AiConde/Fund-Robo-Rover/matlab_code/tag_images/beforebridge_0.6pwm.png

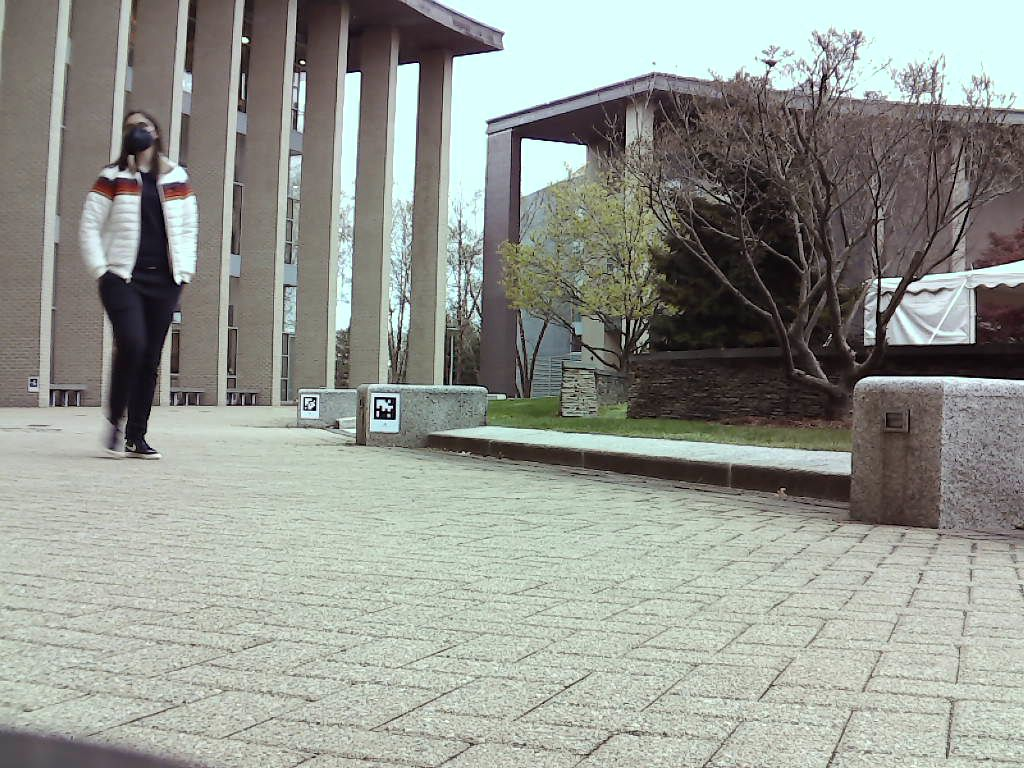
matlab_code/tag_images/beforebridge_0.6pwm.png
