AiConde/Fund-Robo-Rover/matlab_code/tag_images/beforebridge_0.6pwm_2.png

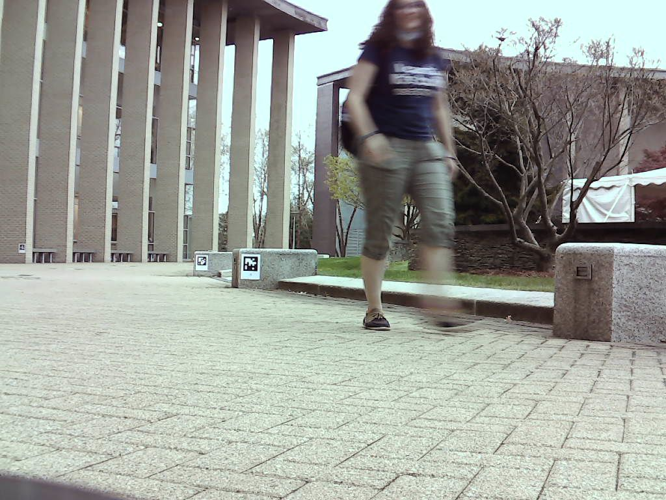
matlab_code/tag_images/beforebridge_0.6pwm_2.png
