AiConde/Fund-Robo-Rover/matlab_code/tag_images/beforebridge_0.55pwm_3.png

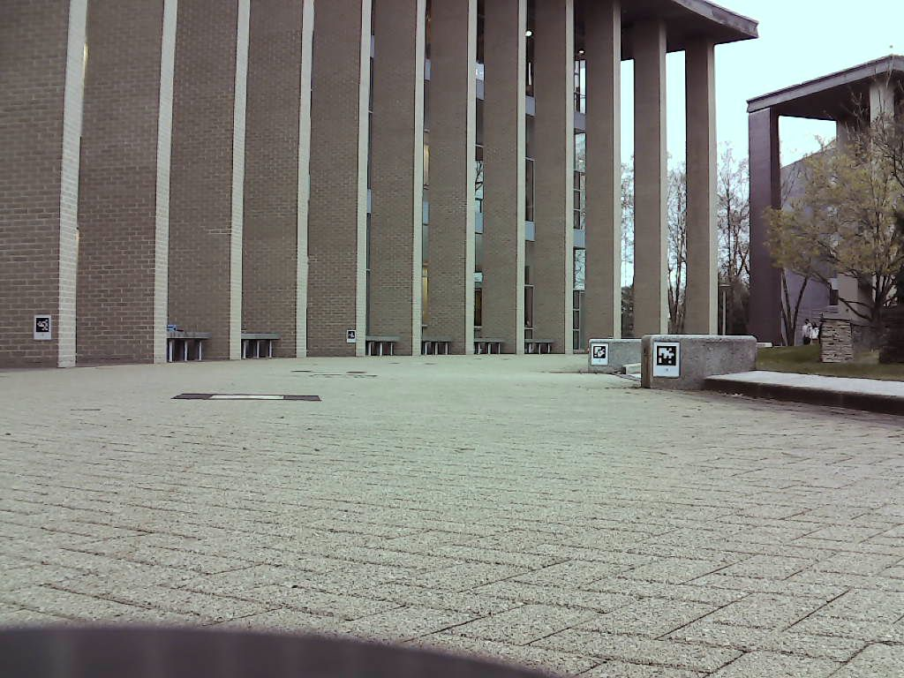
matlab_code/tag_images/beforebridge_0.55pwm_3.png
