AiConde/Fund-Robo-Rover/matlab_code/tag_images/beforecones_0.43pwm_2.png

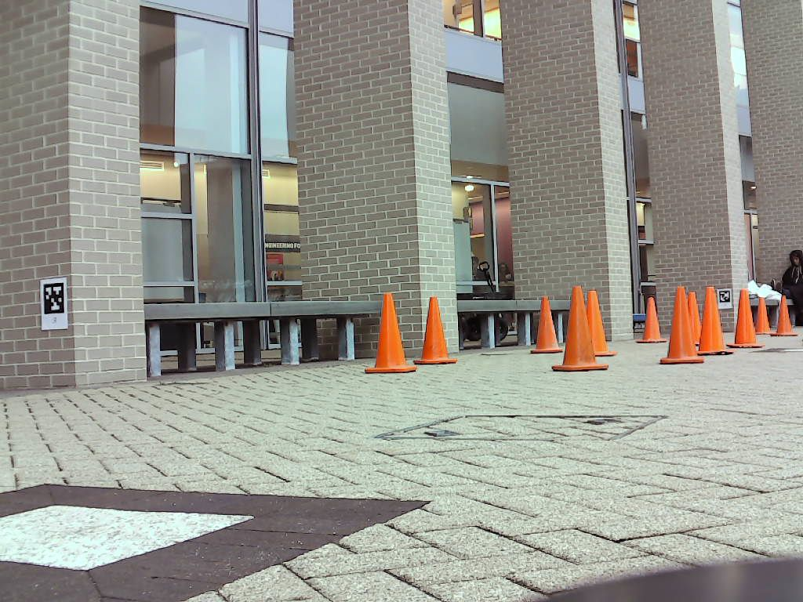
matlab_code/tag_images/beforecones_0.43pwm_2.png
