AiConde/Fund-Robo-Rover/matlab_code/tag_images/block1_0.39pwm.png

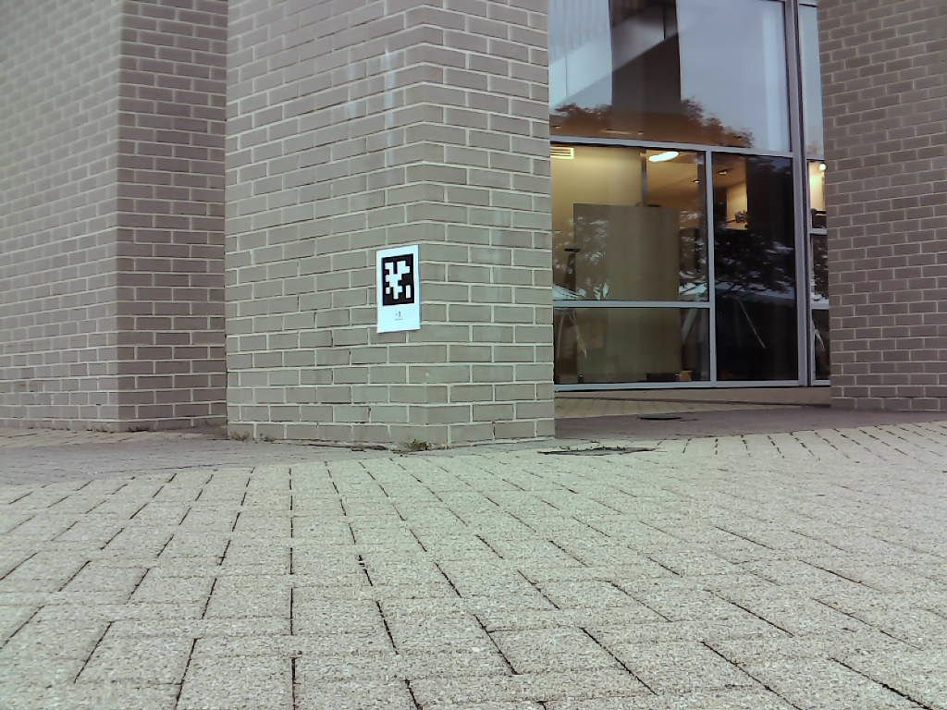
matlab_code/tag_images/block1_0.39pwm.png
