AiConde/Fund-Robo-Rover/matlab_code/tag_images/block1_0.43pwm.png

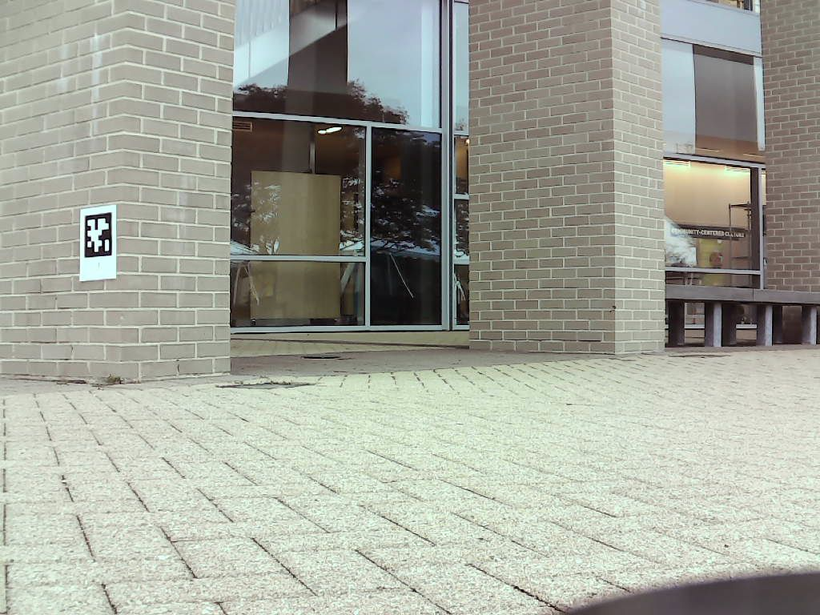
matlab_code/tag_images/block1_0.43pwm.png
