AiConde/Fund-Robo-Rover/matlab_code/tag_images/cj.png

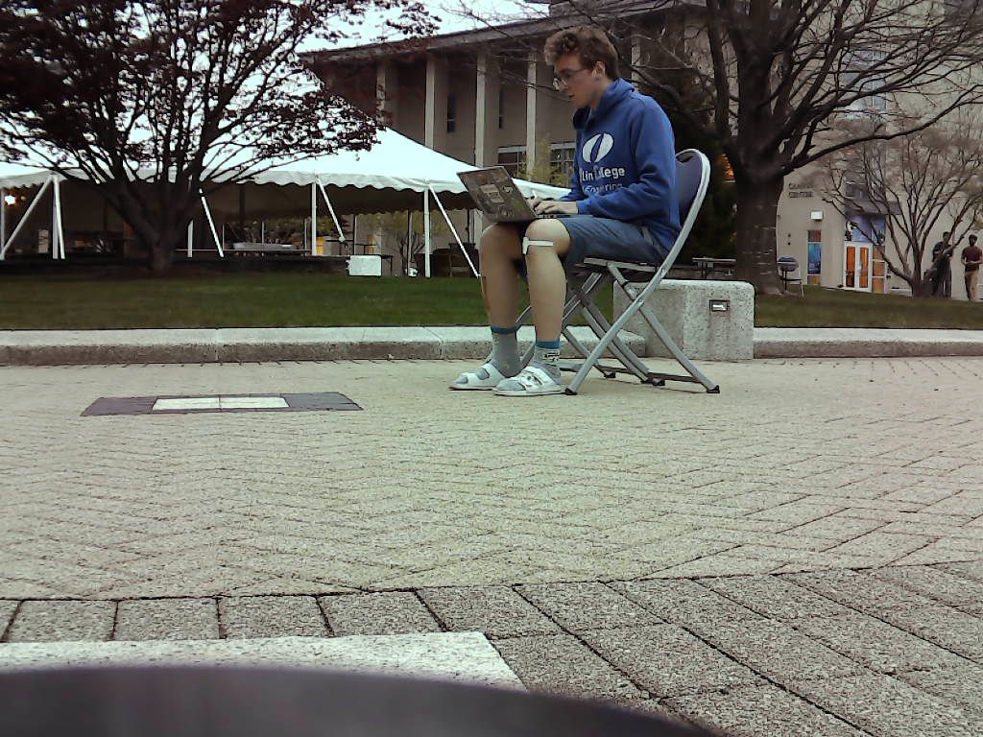
matlab_code/tag_images/cj.png
