AiConde/Fund-Robo-Rover/matlab_code/tag_images/fromdock_0.3pwm_3.png

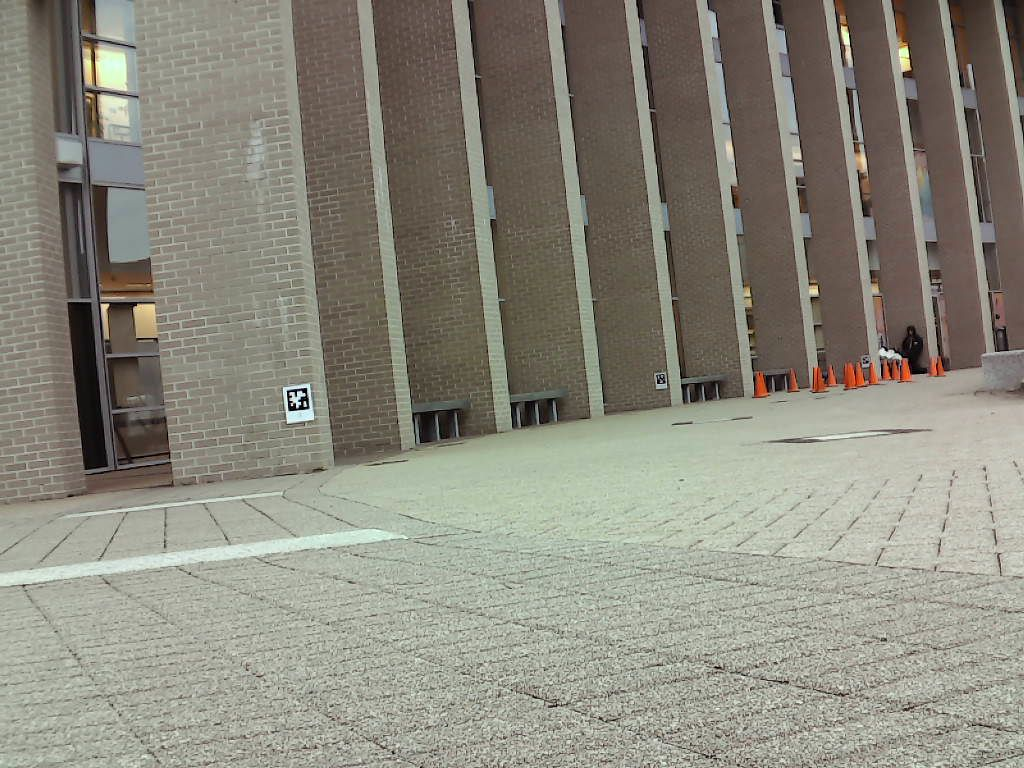
matlab_code/tag_images/fromdock_0.3pwm_3.png
