AiConde/Fund-Robo-Rover/matlab_code/tag_images/origin_north_0.5pwm.png

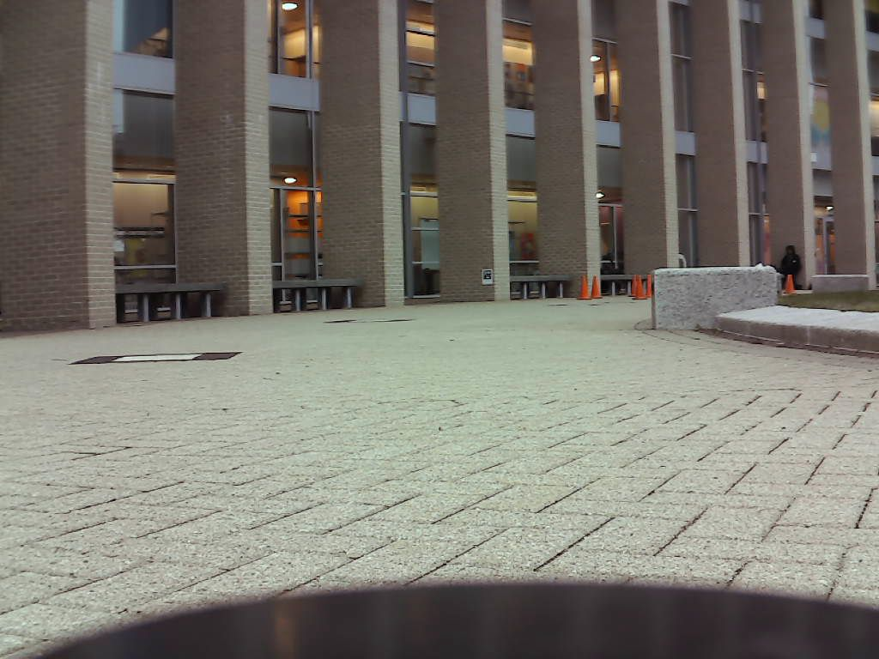
matlab_code/tag_images/origin_north_0.5pwm.png
