AiConde/Fund-Robo-Rover/matlab_code/tag_images/origin_north_0.41pwm_3.png

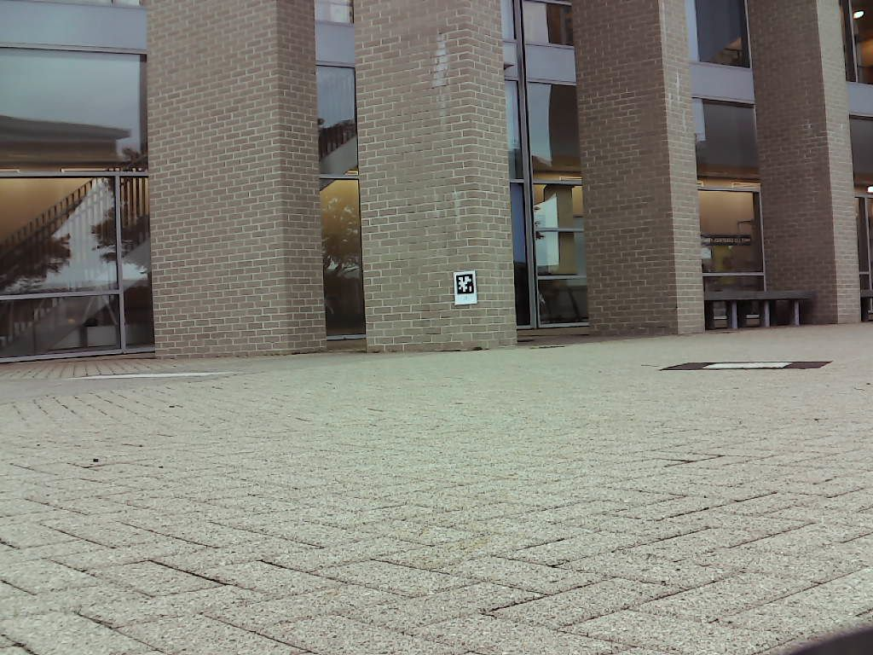
matlab_code/tag_images/origin_north_0.41pwm_3.png
