AiConde/Fund-Robo-Rover/matlab_code/tag_images/viewingdock_0.45pwm.png

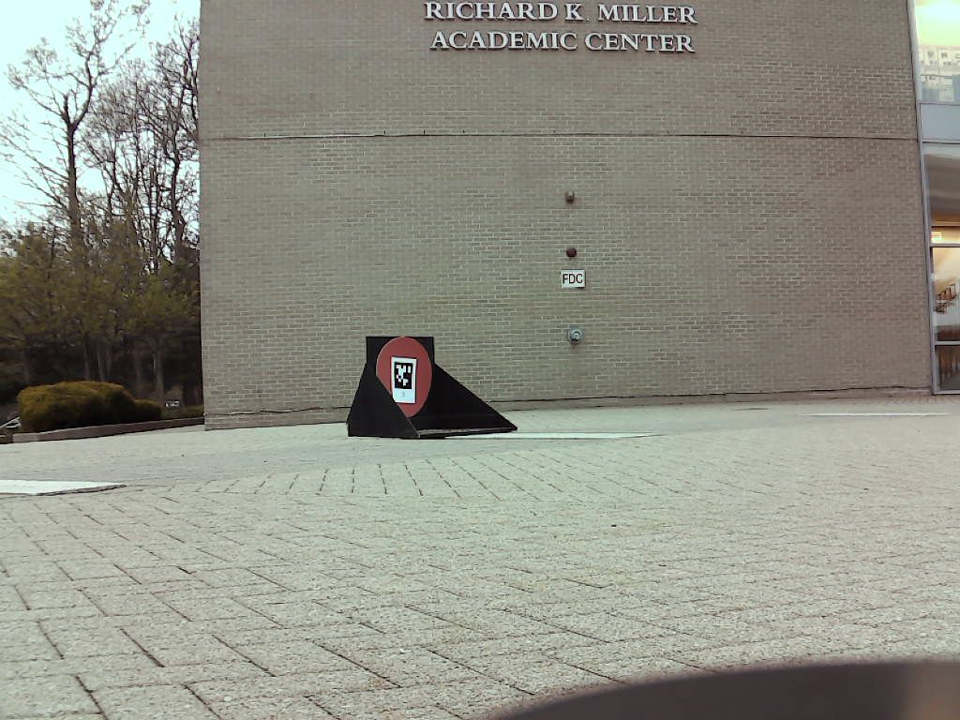
matlab_code/tag_images/viewingdock_0.45pwm.png
