AiConde/Fund-Robo-Rover/CAD files/pan_mechanism.SLDASM

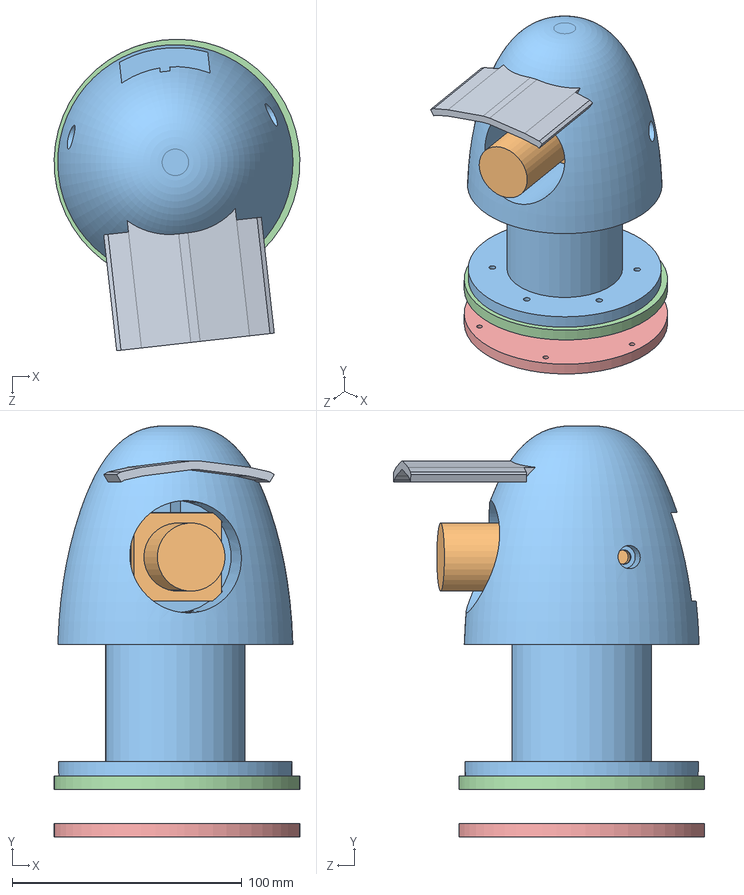
[picture p26: CAD file, 2022-04-15]
CAD files/pan_mechanism.SLDASM
107.0 x 179.0 x 135.7 mm
bottom_pan - Copy
top_pan
among_us
camera
sun
