AiConde/Fund-Robo-Rover/CAD files/ShellCAD/CoverPlate.SLDPRT

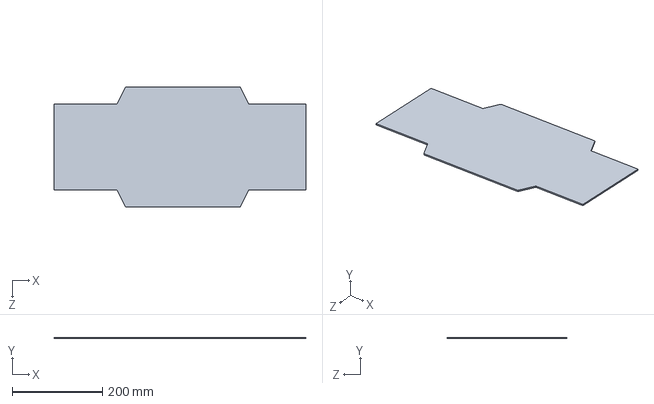
[picture p35: CAD file, 2022-04-15]
CAD files/ShellCAD/CoverPlate.SLDPRT
558.8 x 3.17 x 266.7 mm
