AiConde/Fund-Robo-Rover/CAD files/3D print please/cam_case.STL

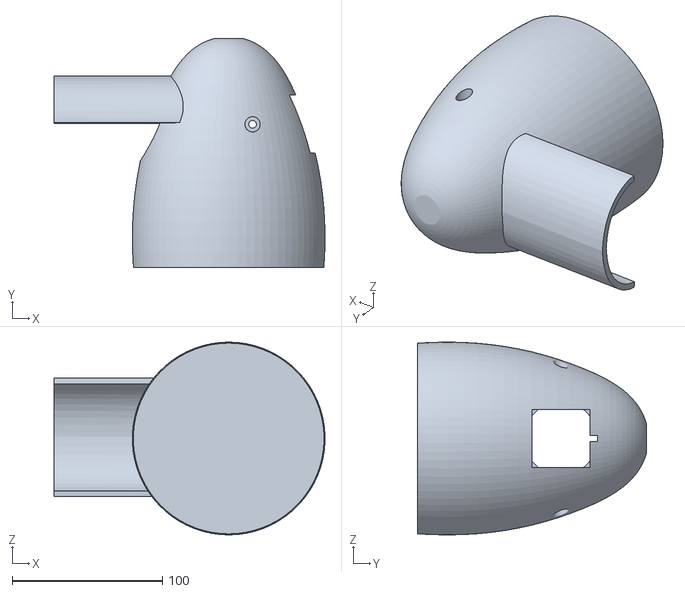
[picture p36: CAD file, 2022-04-15]
CAD files/3D print please/cam_case.STL
180.5 x 152.4 x 128.4
