AiConde/Fund-Robo-Rover/CAD files/3D print please/For Dave/camera_sun-shield.STL

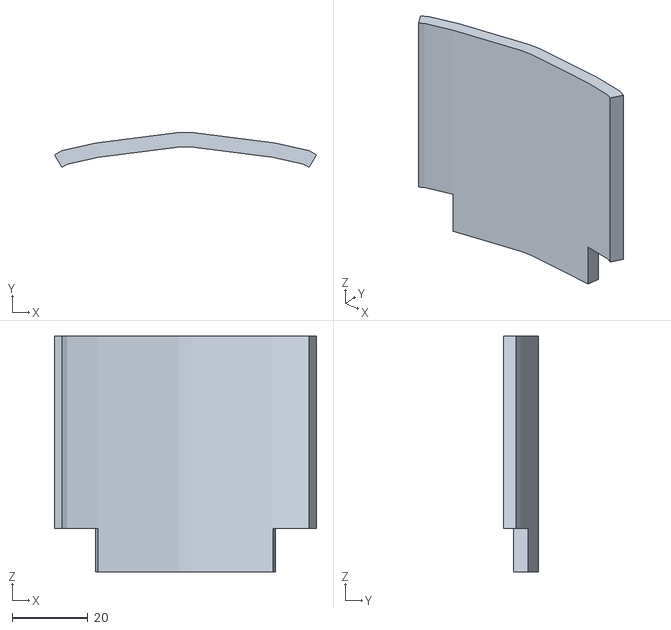
[picture p37: CAD file, 2022-04-15]
CAD files/3D print please/For Dave/camera_sun-shield.STL
69.1 x 9.17 x 62.2
