AiConde/Fund-Robo-Rover/CAD files/ShellCAD/BatteryCase/BatteryCaseEnd.SLDPRT

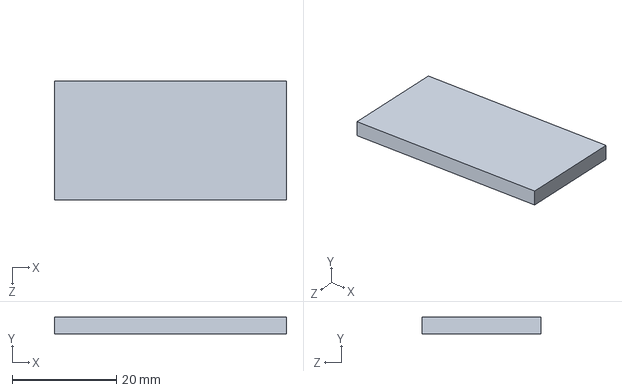
[picture p38: CAD file, 2022-04-13]
CAD files/ShellCAD/BatteryCase/BatteryCaseEnd.SLDPRT
44.5 x 3.17 x 22.9 mm
