AiConde/Fund-Robo-Rover/CAD files/ShellCAD/WiringHoles/LowerPanelWide.SLDPRT

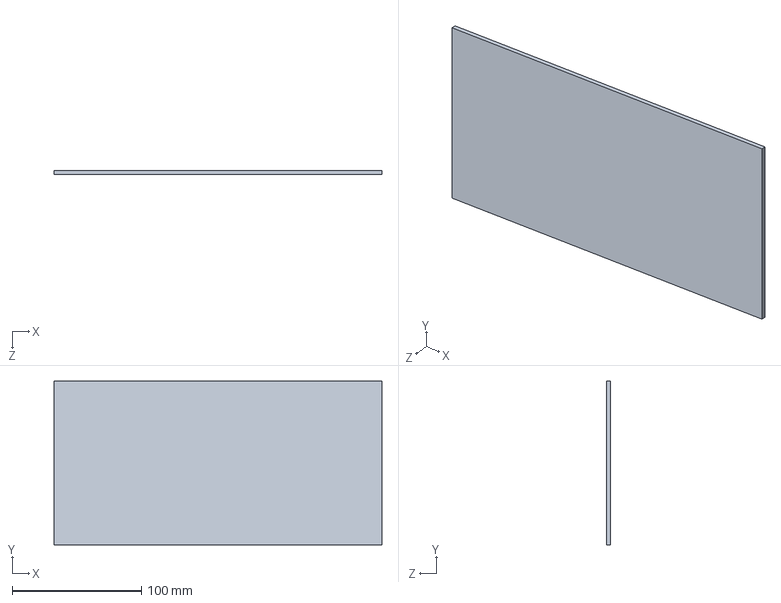
[picture p39: CAD file, 2022-04-15]
CAD files/ShellCAD/WiringHoles/LowerPanelWide.SLDPRT
254.0 x 127.0 x 3.17 mm
