AiConde/Fund-Robo-Rover/CAD files/3D print please/For Dave/camera_case.STL

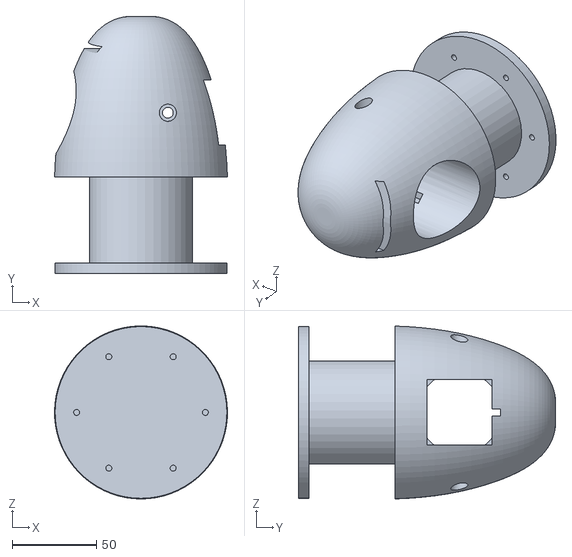
[picture p40: CAD file, 2022-04-15]
CAD files/3D print please/For Dave/camera_case.STL
102.4 x 152.4 x 102.4
