AiConde/Fund-Robo-Rover/CAD files/3D print please/LIDAR_top.STL

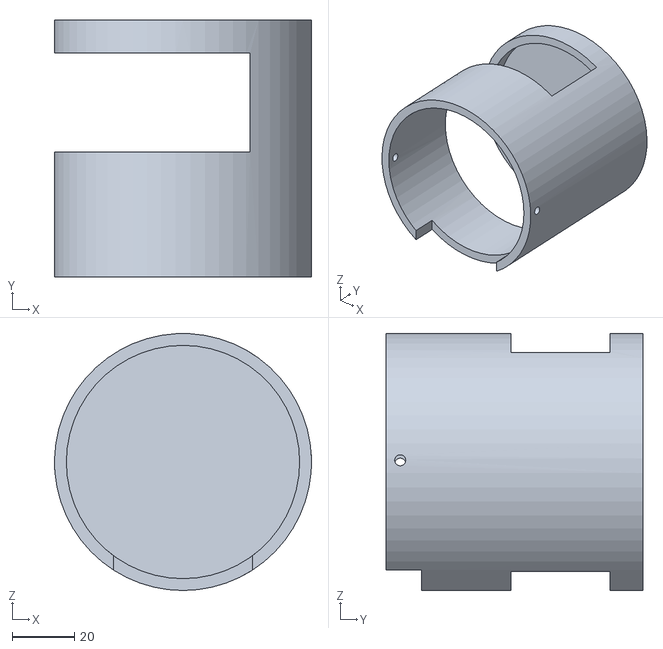
[picture p41: CAD file, 2022-04-13]
CAD files/3D print please/LIDAR_top.STL
82.5 x 82.5 x 82.5
