AiConde/Fund-Robo-Rover/CAD files/ShellCAD/WiringHoles/UpperFront.SLDPRT

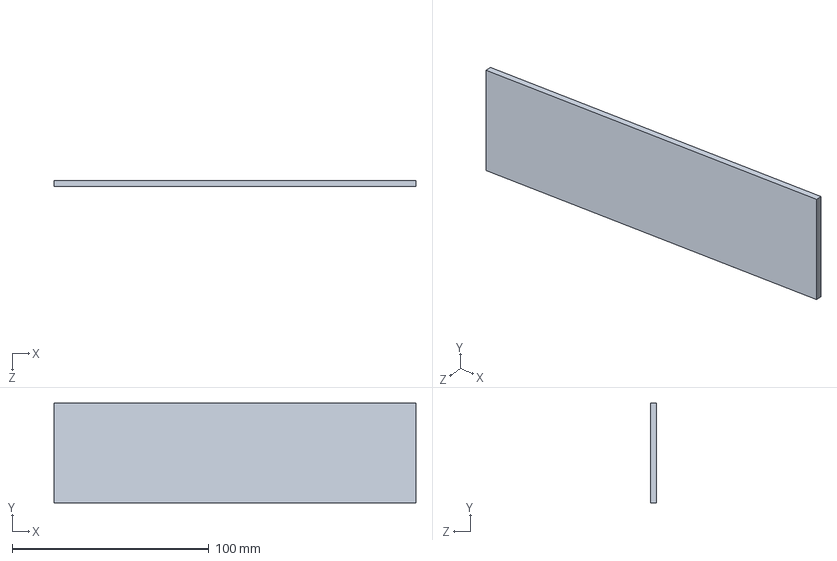
[picture p42: CAD file, 2022-04-15]
CAD files/ShellCAD/WiringHoles/UpperFront.SLDPRT
184.1 x 50.8 x 3.17 mm
