AiConde/Fund-Robo-Rover/CAD files/3D print please/LIDAR_base.STL

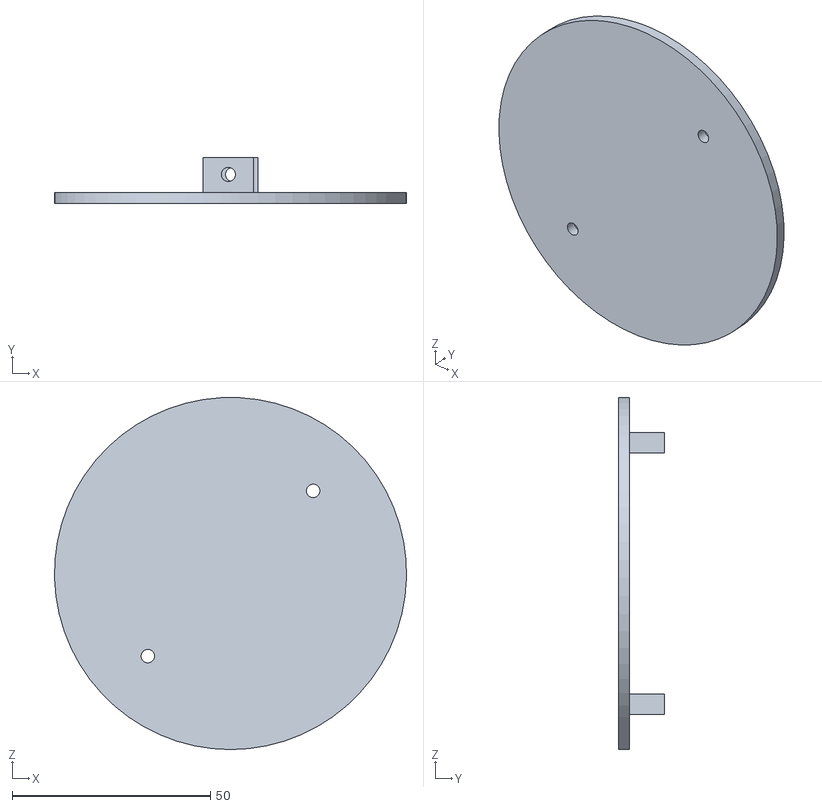
[picture p43: CAD file, 2022-04-13]
CAD files/3D print please/LIDAR_base.STL
88.9 x 11.7 x 88.9
