AiConde/Fund-Robo-Rover/CAD files/Attachment Leg.SLDPRT

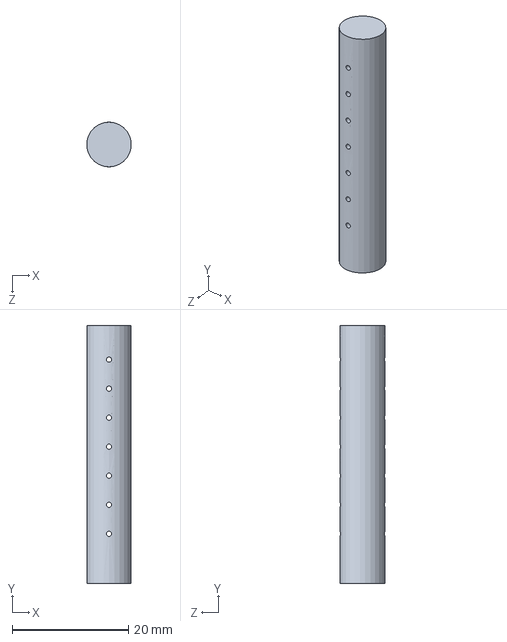
[picture p44: CAD file, 2022-04-15]
CAD files/Attachment Leg.SLDPRT
7.64 x 44.5 x 7.70 mm
