AiConde/Fund-Robo-Rover/CAD files/ShellCAD/BatteryCase/BatteryCaseShort.SLDPRT

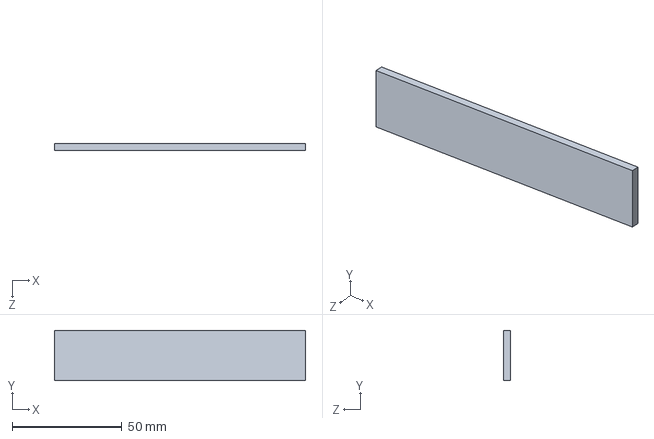
[picture p45: CAD file, 2022-04-13]
CAD files/ShellCAD/BatteryCase/BatteryCaseShort.SLDPRT
114.3 x 22.9 x 3.17 mm
