AiConde/Fund-Robo-Rover/CAD files/LIDAR_top_sun.SLDPRT

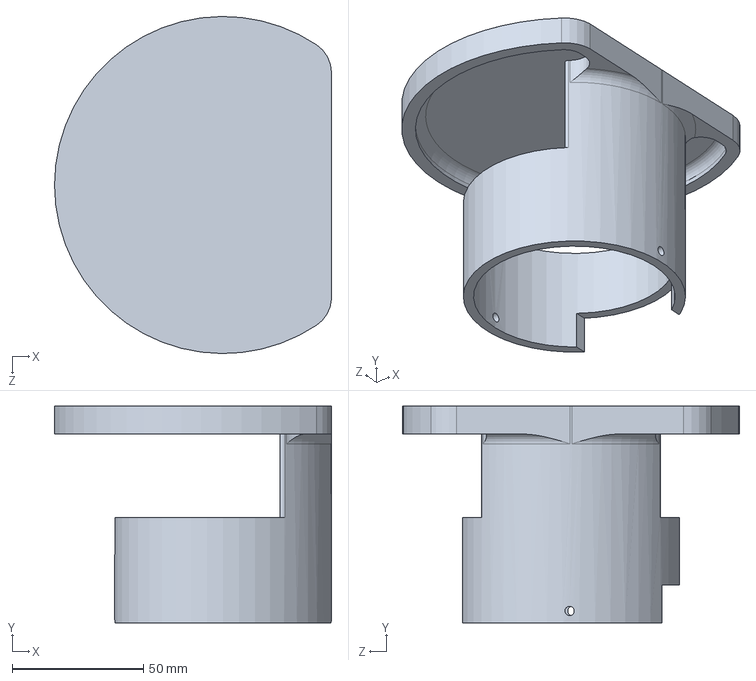
[picture p46: CAD file, 2022-04-15]
CAD files/LIDAR_top_sun.SLDPRT
105.4 x 82.5 x 128.3 mm
