AiConde/Fund-Robo-Rover/CAD files/top_pan.SLDPRT

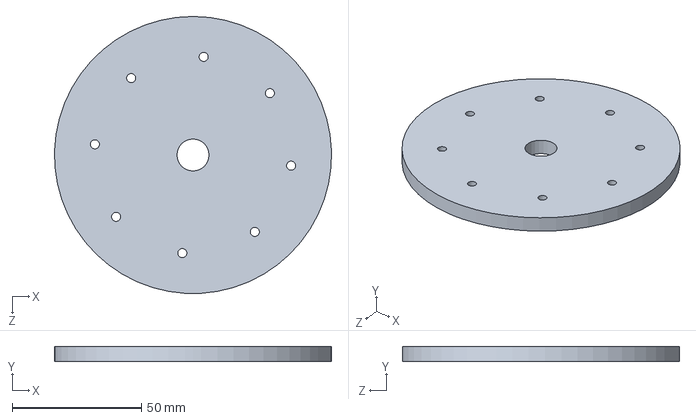
[picture p47: CAD file, 2022-04-15]
CAD files/top_pan.SLDPRT
107.0 x 5.96 x 107.1 mm
