AiConde/Fund-Robo-Rover/CAD files/shade.SLDPRT

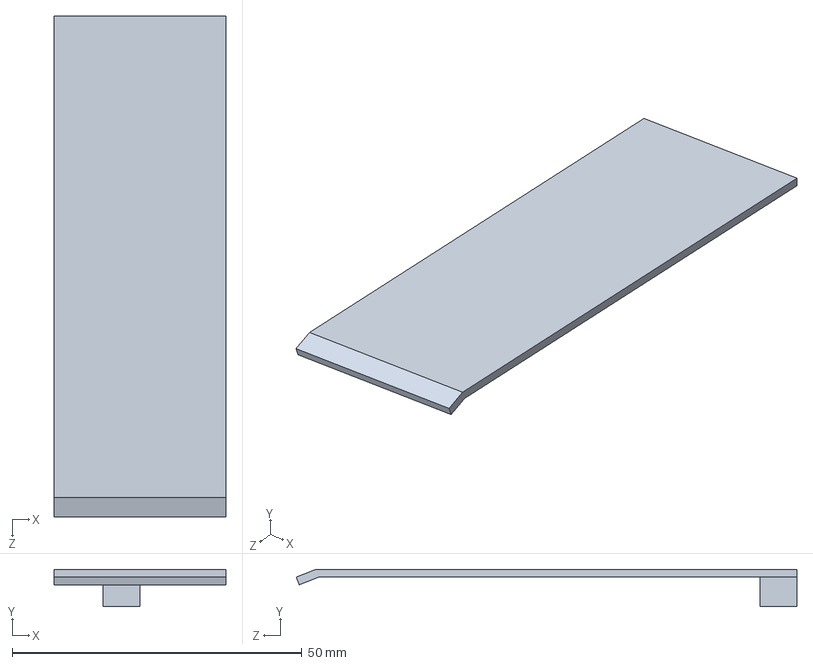
[picture p48: CAD file, 2022-04-15]
CAD files/shade.SLDPRT
29.7 x 6.41 x 86.4 mm
