AiConde/Fund-Robo-Rover/CAD files/camera.SLDPRT

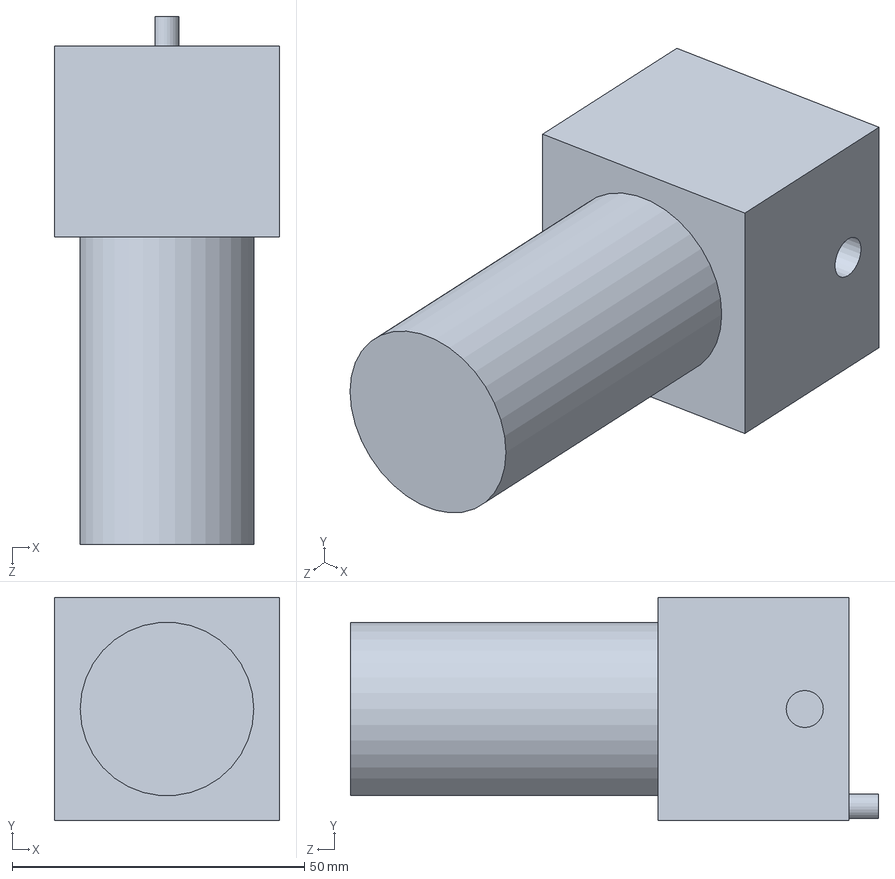
[picture p49: CAD file, 2022-04-15]
CAD files/camera.SLDPRT
38.5 x 38.2 x 90.4 mm
