AiConde/Fund-Robo-Rover/CAD files/ShellCAD/WiringHoles/UpperAngleWallLarge.SLDPRT

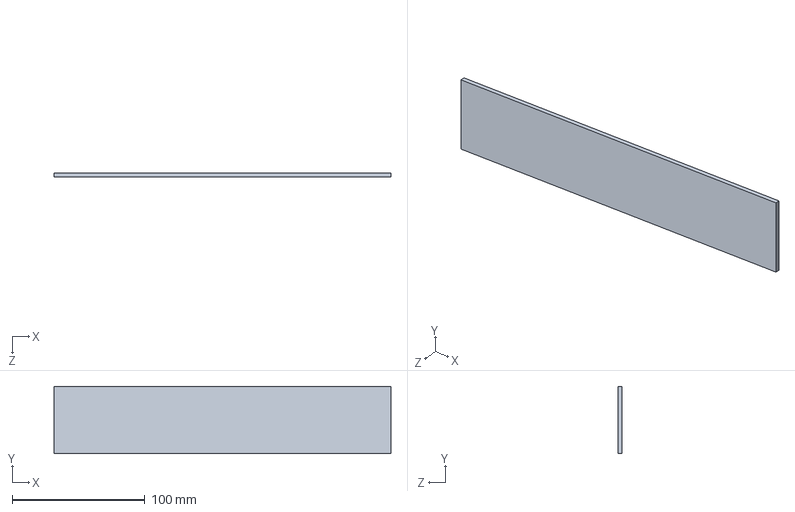
[picture p50: CAD file, 2022-04-13]
CAD files/ShellCAD/WiringHoles/UpperAngleWallLarge.SLDPRT
254.0 x 50.8 x 3.17 mm
