AiConde/Fund-Robo-Rover/CAD files/ShellCAD/WiringHoles/LidarLift.SLDPRT

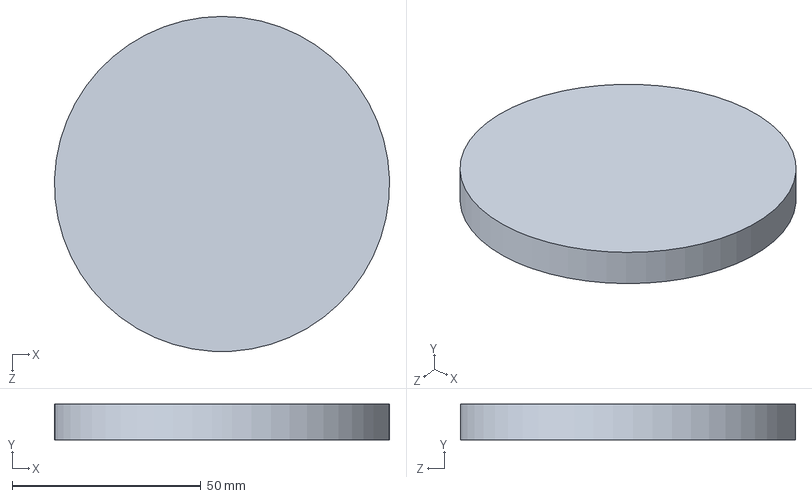
[picture p51: CAD file, 2022-04-13]
CAD files/ShellCAD/WiringHoles/LidarLift.SLDPRT
88.9 x 9.53 x 88.9 mm
