AiConde/Fund-Robo-Rover/CAD files/ShellCAD/WiringHoles/Part9.SLDPRT

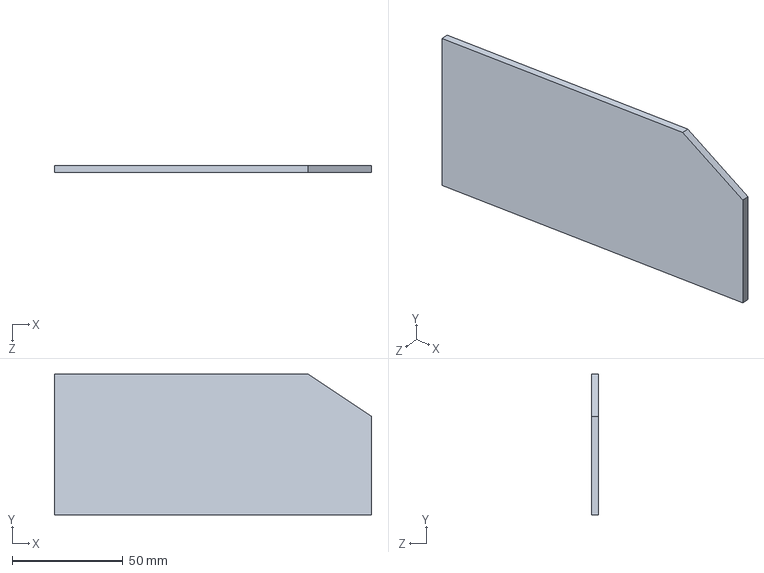
[picture p52: CAD file, 2022-04-13]
CAD files/ShellCAD/WiringHoles/Part9.SLDPRT
142.9 x 63.5 x 3.17 mm
