AiConde/Fund-Robo-Rover/CAD files/ShellCAD/WiringHoles/LowerPanelThin.SLDPRT

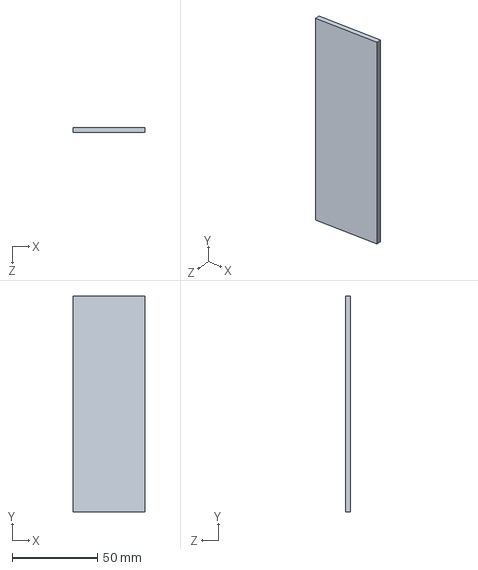
[picture p53: CAD file, 2022-04-13]
CAD files/ShellCAD/WiringHoles/LowerPanelThin.SLDPRT
42.6 x 127.0 x 3.17 mm
