AiConde/Fund-Robo-Rover/CAD files/cam_case.SLDPRT

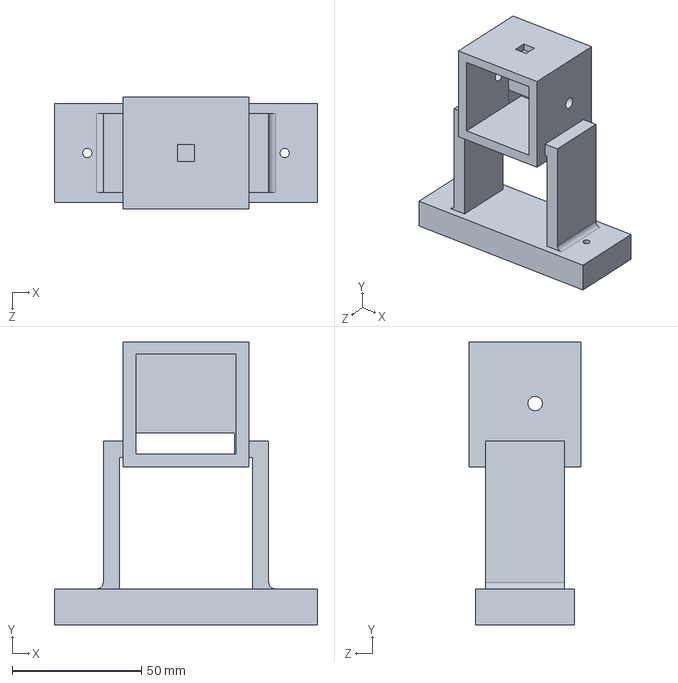
[picture p54: CAD file, 2022-04-15]
CAD files/cam_case.SLDPRT
101.6 x 109.3 x 43.3 mm
