AiConde/Fund-Robo-Rover/CAD files/ShellCAD/WiringHoles/UpperRearWall.SLDPRT

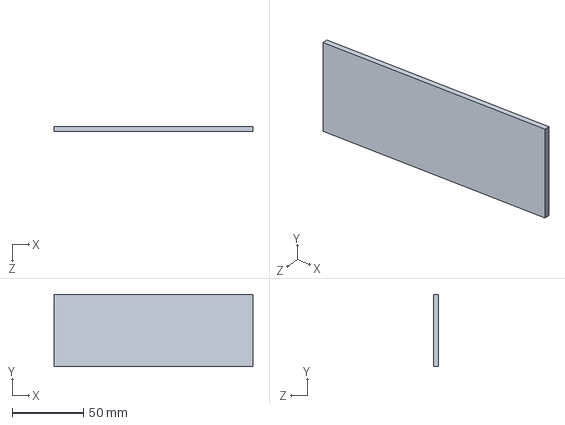
[picture p55: CAD file, 2022-04-13]
CAD files/ShellCAD/WiringHoles/UpperRearWall.SLDPRT
139.7 x 50.8 x 3.17 mm
