AiConde/Fund-Robo-Rover/CAD files/LIDAR.SLDPRT

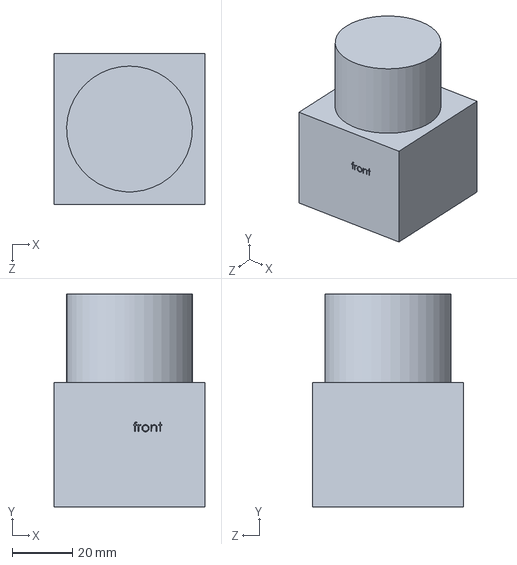
[picture p56: CAD file, 2022-04-13]
CAD files/LIDAR.SLDPRT
50.0 x 70.6 x 50.0 mm
