AiConde/Fund-Robo-Rover/CAD files/ShellCAD/WiringHoles/UpperFrontWall.SLDPRT

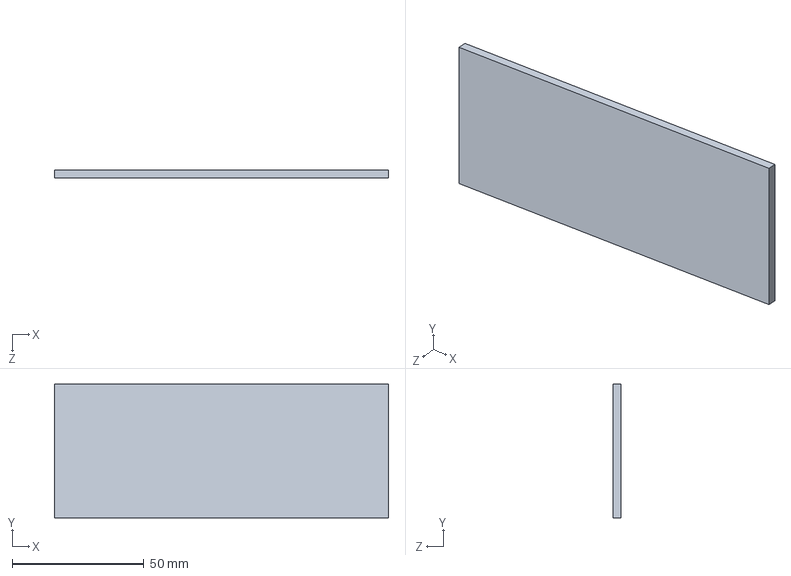
[picture p57: CAD file, 2022-04-13]
CAD files/ShellCAD/WiringHoles/UpperFrontWall.SLDPRT
127.0 x 50.8 x 3.17 mm
