AiConde/Fund-Robo-Rover/CAD files/GPS Antenna.SLDPRT

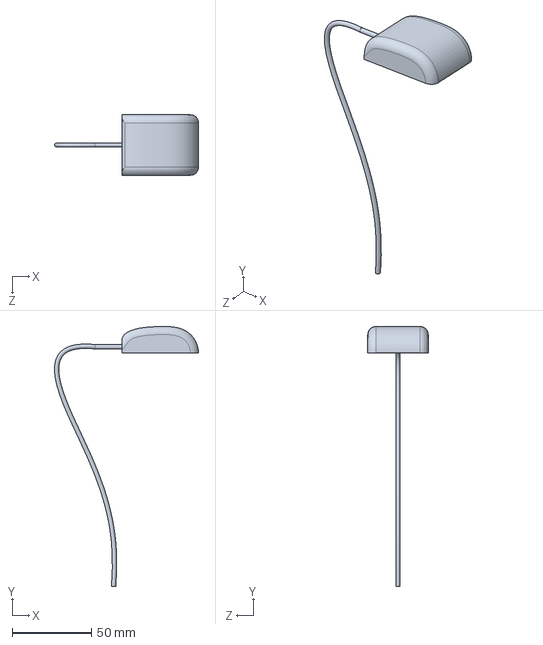
[picture p58: CAD file, 2022-04-12]
CAD files/GPS Antenna.SLDPRT
90.7 x 163.7 x 38.1 mm
