AiConde/Fund-Robo-Rover/CAD files/sonar.SLDPRT

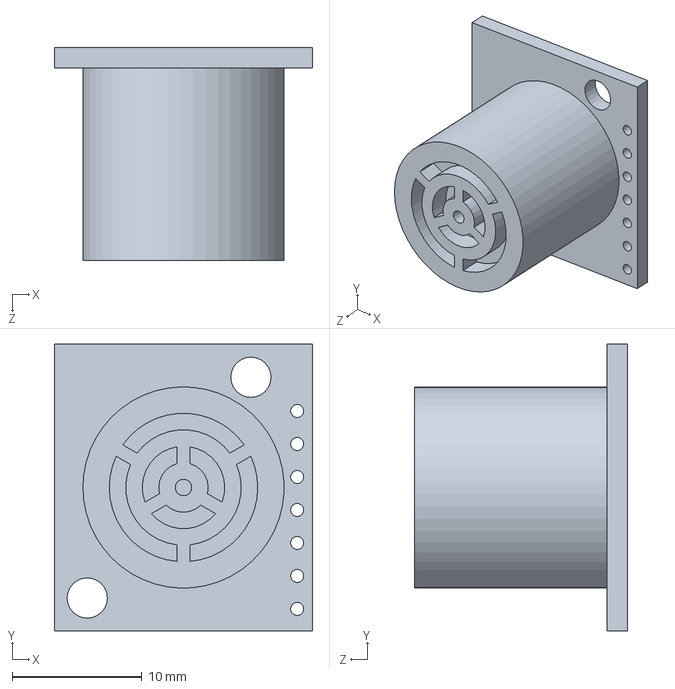
[picture p59: CAD file, 2022-04-12]
CAD files/sonar.SLDPRT
19.9 x 22.1 x 16.4 mm
