AiConde/Fund-Robo-Rover/CAD files/e-stop.SLDPRT

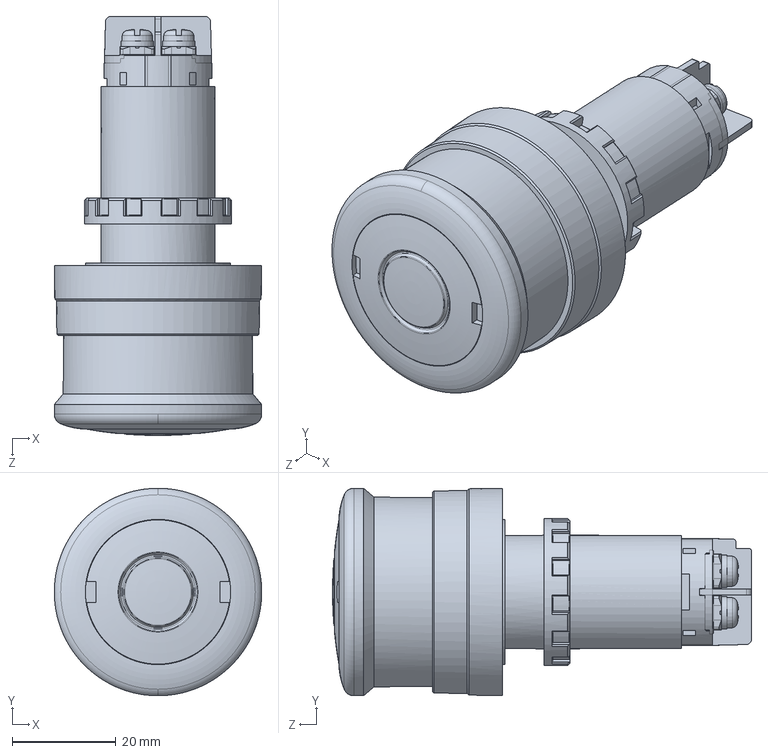
[picture p60: CAD file, 2022-04-12]
CAD files/e-stop.SLDPRT
40.0 x 40.0 x 80.8 mm
