AiConde/Fund-Robo-Rover/CAD files/Base.SLDPRT

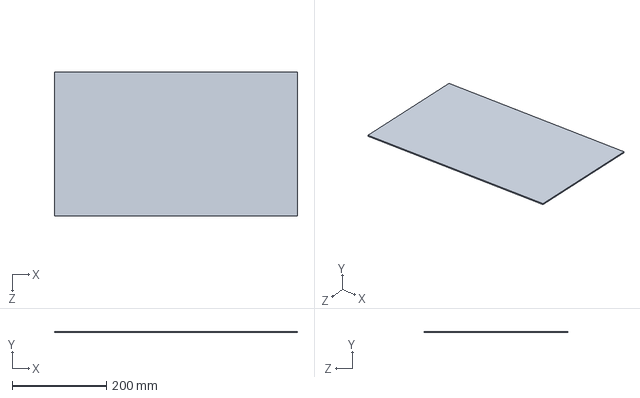
[picture p61: CAD file, 2022-04-12]
CAD files/Base.SLDPRT
514.3 x 2.79 x 304.8 mm
