AiConde/Fund-Robo-Rover/CAD files/VenomBattery.SLDPRT

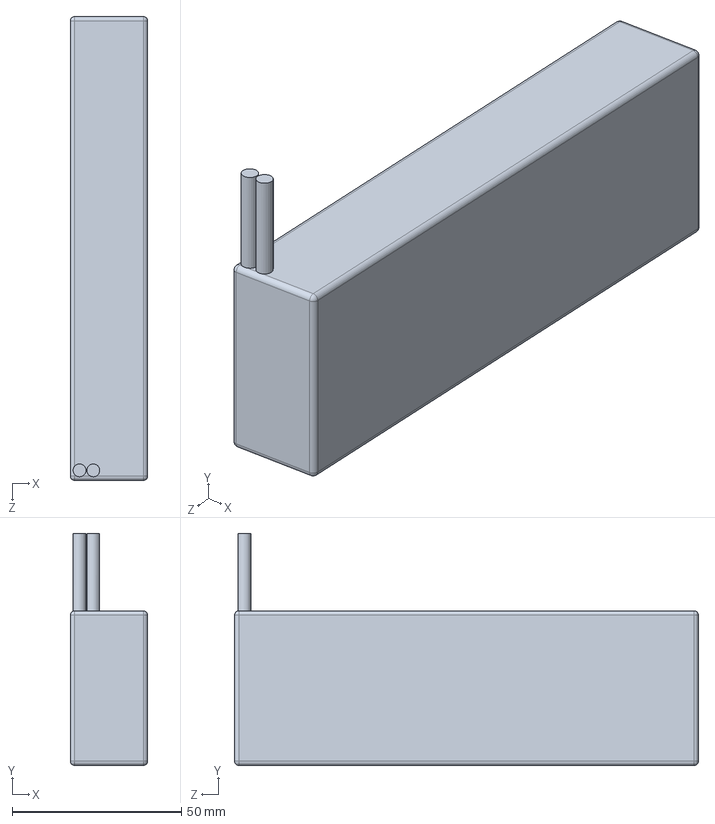
[picture p62: CAD file, 2022-04-12]
CAD files/VenomBattery.SLDPRT
22.9 x 68.6 x 137.2 mm
