AiConde/Fund-Robo-Rover/CAD files/hex_hood.SLDPRT

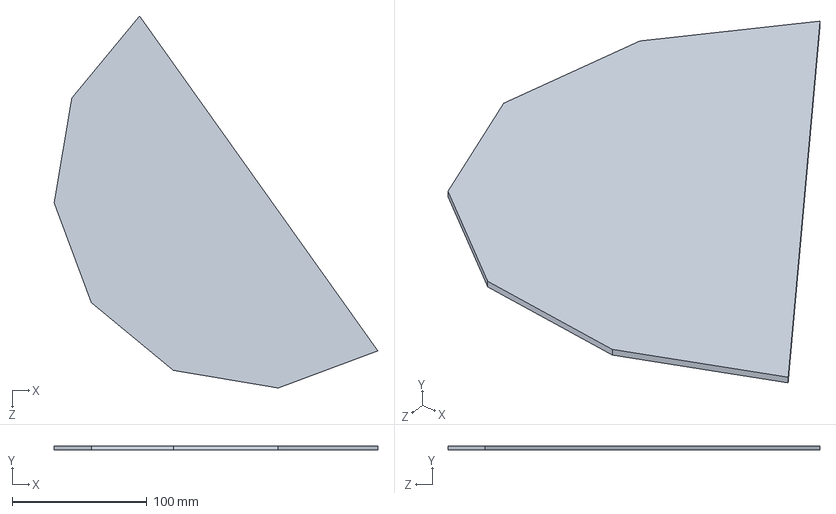
[picture p63: CAD file, 2022-04-12]
CAD files/hex_hood.SLDPRT
240.1 x 2.79 x 275.9 mm
