AiConde/Fund-Robo-Rover/CAD files/servo.SLDPRT

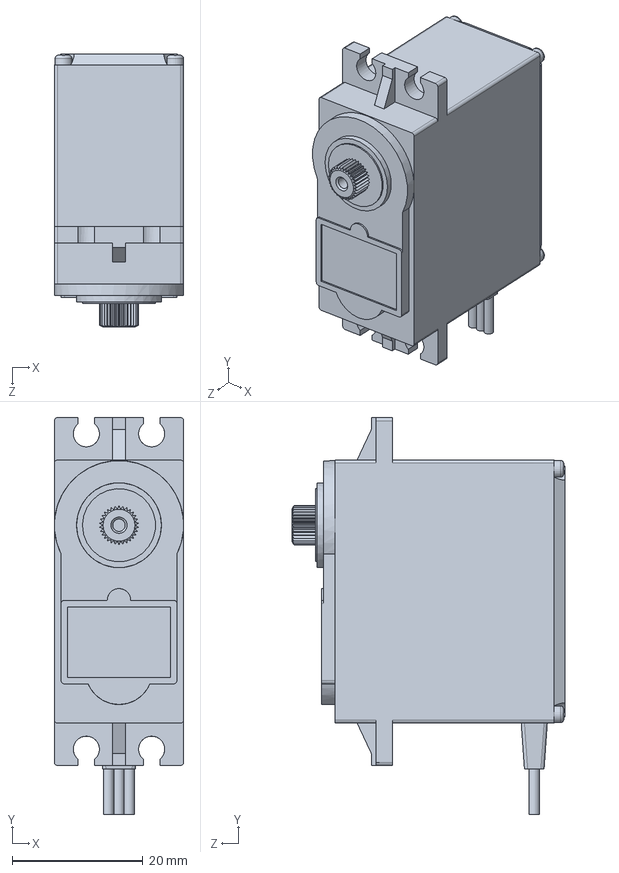
[picture p64: CAD file, 2022-04-12]
CAD files/servo.SLDPRT
19.8 x 60.8 x 41.9 mm
