AiConde/Fund-Robo-Rover/CAD files/NUC.SLDPRT

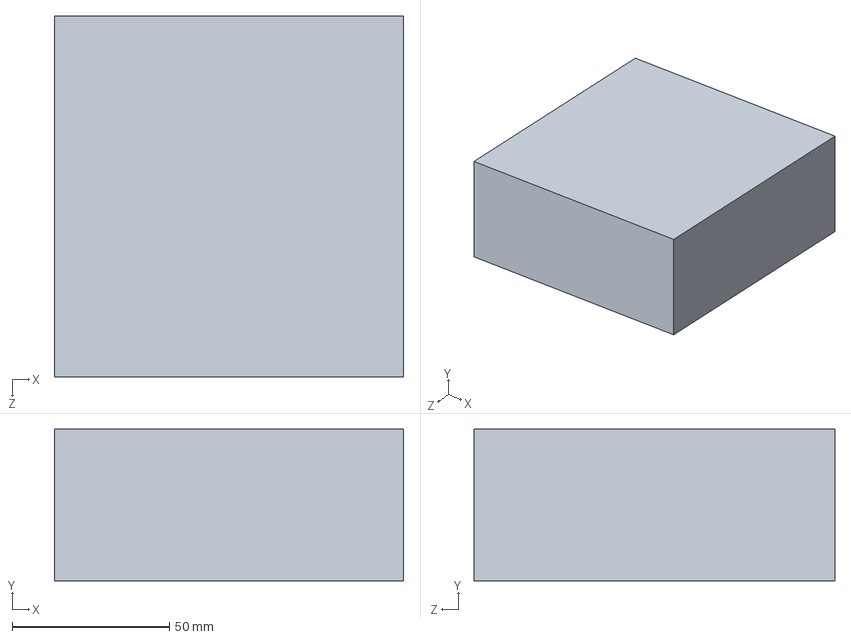
[picture p65: CAD file, 2022-04-12]
CAD files/NUC.SLDPRT
111.0 x 48.3 x 114.8 mm
