AiConde/Fund-Robo-Rover/CAD files/IR.SLDPRT

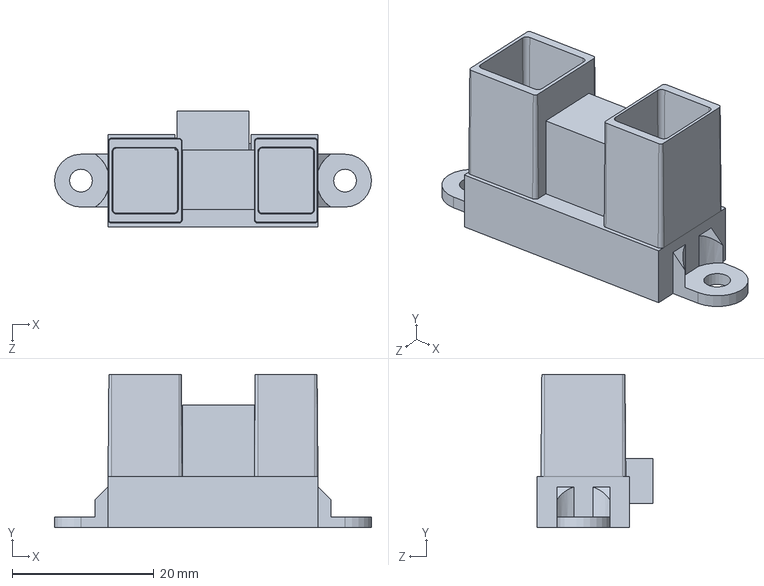
[picture p66: CAD file, 2022-04-12]
CAD files/IR.SLDPRT
44.8 x 21.6 x 16.4 mm
