AiConde/Fund-Robo-Rover/CAD files/hex_IR.SLDPRT

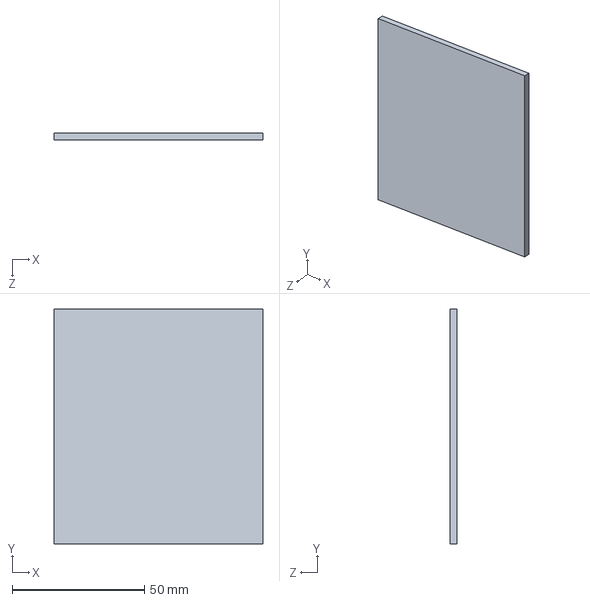
[picture p67: CAD file, 2022-04-12]
CAD files/hex_IR.SLDPRT
79.0 x 88.9 x 2.79 mm
