AiConde/Fund-Robo-Rover/matlab_code/camera_calibration/calib_1024x768/my_photo-16.jpg

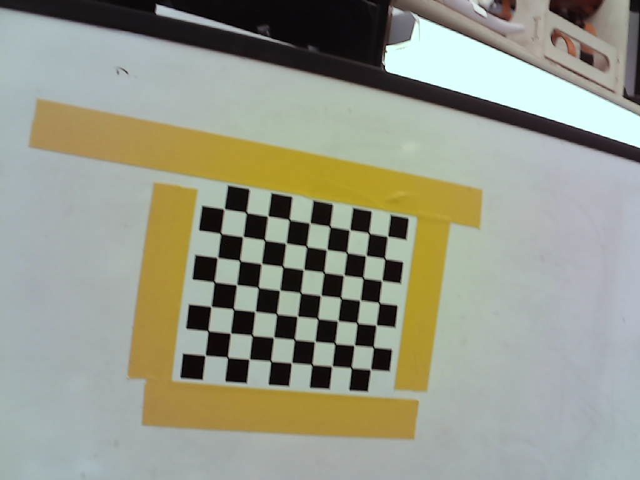
matlab_code/camera_calibration/calib_1024x768/my_photo-16.jpg
