AiConde/Fund-Robo-Rover/matlab_code/camera_calibration/calib_3268x2448/my_photo-10.jpg

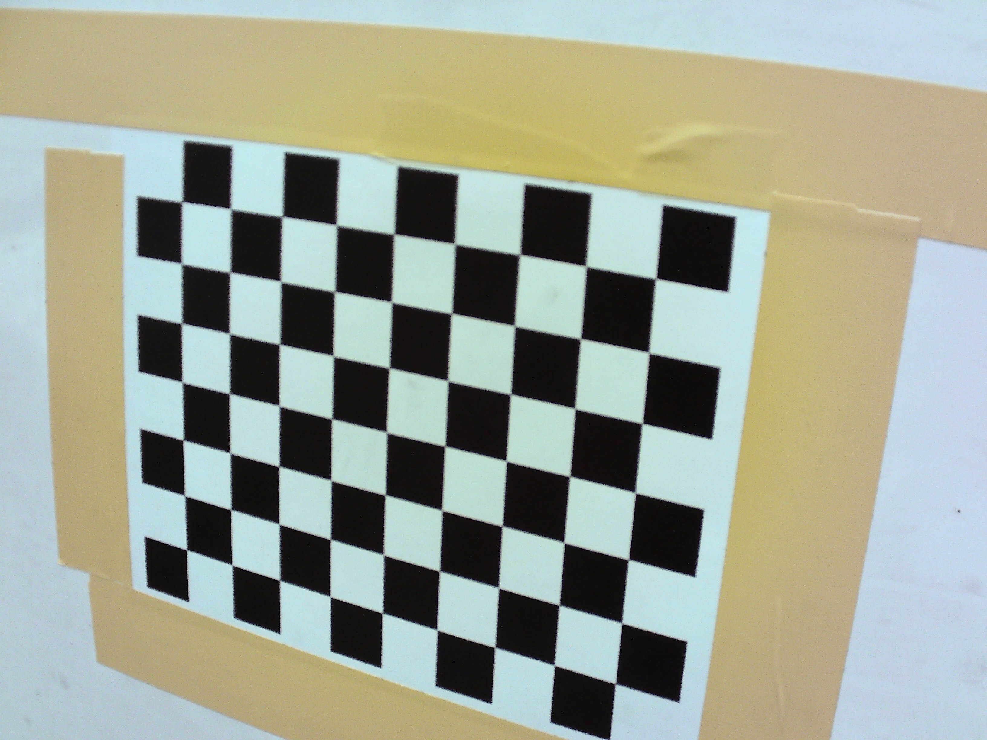
matlab_code/camera_calibration/calib_3268x2448/my_photo-10.jpg
