AiConde/Fund-Robo-Rover/matlab_code/test_data/oval_satellite.png

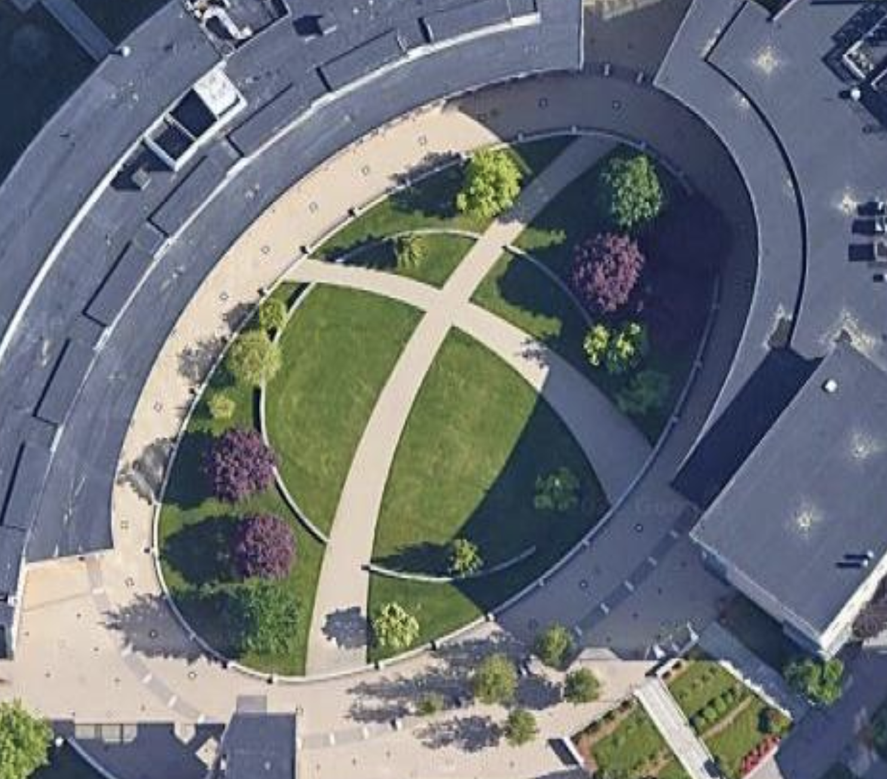
matlab_code/test_data/oval_satellite.png
