AiConde/Fund-Robo-Rover/ros_files/m8u_rover.yaml

# Configuration Settings for C94-M8P device

debug: 1                    # Range 0-4 (0 means no debug statements will print)

save:
  mask: 3103                # Save I/O, Message, INF Message, Nav, Receiver 
                            # Manager, Antenna, and Logging Configuration
  device: 4                 # Save to EEPROM

device: /dev/ublox_gps
frame_id: m8u 
rate: 4                     # in Hz
nav_rate: 4                 # [# of measurement cycles], recommended 1 Hz, may 
                            # be either 5 Hz (Dual constellation) or 
                            # 8 Hz (GPS only)
dynamic_model: 0    # Airborne < 2G, 2D fix not supported (3D only), 
                            # Max Alt: 50km
                            # Max Horizontal Velocity: 250 m/s, 
                            # Max Vertical Velocity: 100 m/s
fix_mode: 3 
enable_ppp: true           # Not supported by C94-M8P
dr_limit: 1

uart1:
  baudrate: 115200           # C94-M8P specific
  in: 16                    # RTCM 3
  out: 16                    # No UART out for rover

gnss:
  glonass: true             # Supported by C94-M8P
  beidou: false             # Supported by C94-M8P
  qzss: false               # Supported by C94-M8P

dgnss_mode: 3               # Fixed mode

inf: 
  all: true                   # Whether to display all INF messages in console

# Enable u-blox message publishers
publish:
  all: true
  esf: true
  aid:
    hui: false
  nav:
    posecef: false
